tomatoesong/HE_Leverless/images/51Fhb4z4ydL._SL1200_.jpg

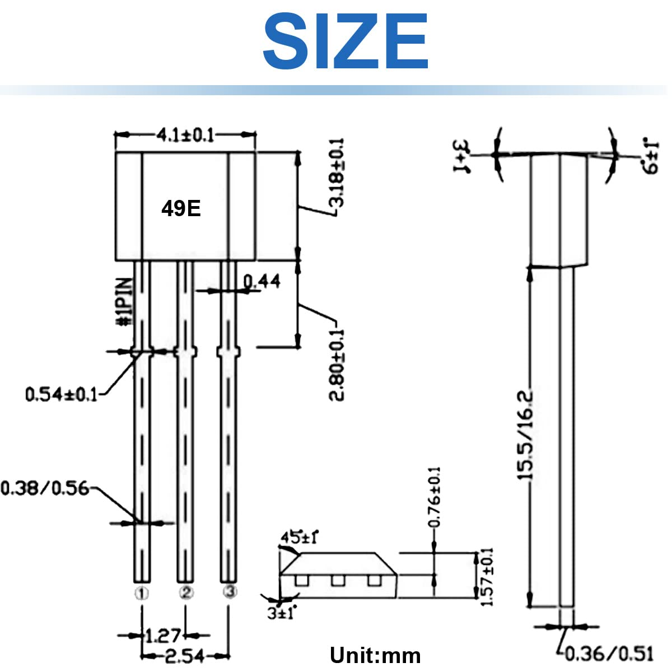
images/51Fhb4z4ydL._SL1200_.jpg
