tomatoesong/HE_Leverless/images/Scanned_20250402-2004.jpg

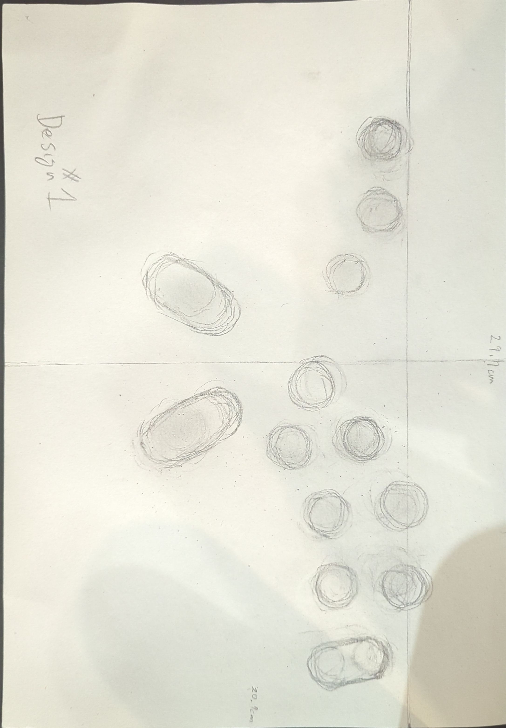
images/Scanned_20250402-2004.jpg
